Selim-Emir-Can/RoMeLa-YORI-Team-ModularGasSensor/Modular-Gas-Sensor-CAD-files/GS-M3.SLDPRT

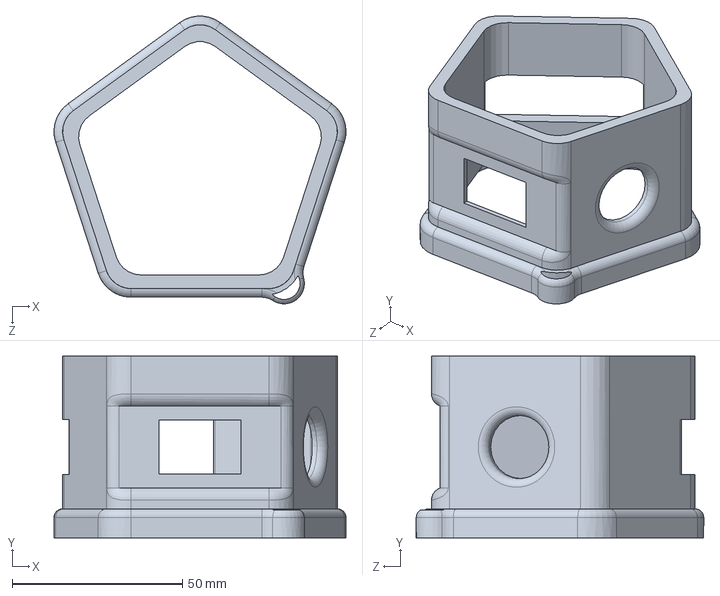
[picture p11: CAD file, 2022-09-08]
Modular-Gas-Sensor-CAD-files/GS-M3.SLDPRT
85.8 x 53.3 x 84.5 mm
