Selim-Emir-Can/RoMeLa-YORI-Team-ModularGasSensor/Modular-Gas-Sensor-CAD-files/Flexible coolant conexion.SLDPRT

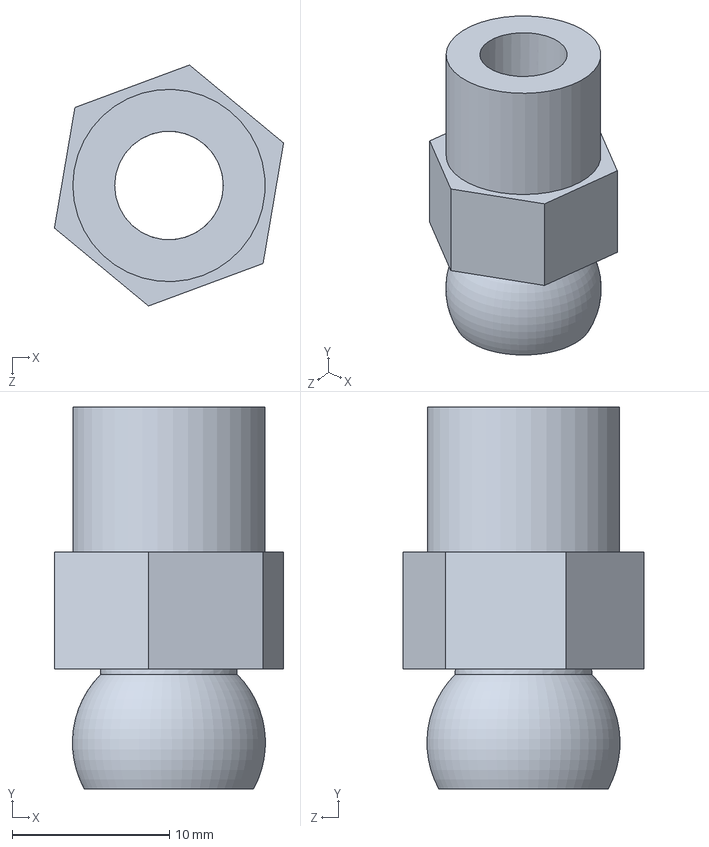
[picture p12: CAD file, 2022-09-08]
Modular-Gas-Sensor-CAD-files/Flexible coolant conexion.SLDPRT
14.6 x 24.3 x 15.3 mm
