Selim-Emir-Can/RoMeLa-YORI-Team-ModularGasSensor/Modular-Gas-Sensor-CAD-files/GS-M2.SLDPRT

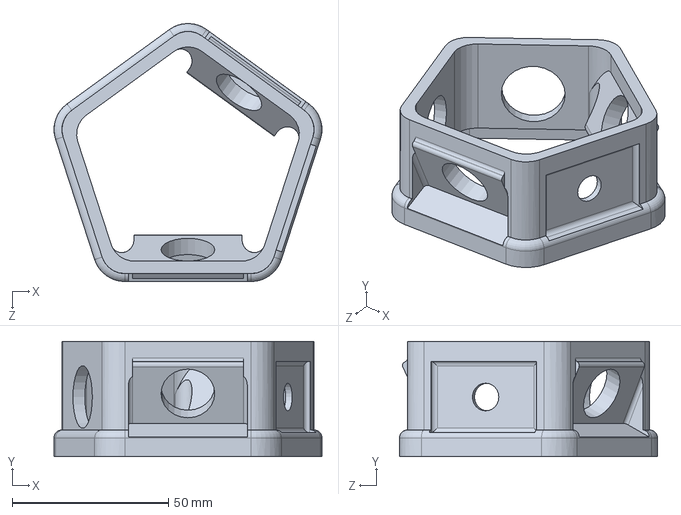
[picture p13: CAD file, 2022-09-08]
Modular-Gas-Sensor-CAD-files/GS-M2.SLDPRT
85.8 x 36.8 x 82.6 mm
